daokoa/SoleSense2026/firmware/SoleSenseV2/state.h

// =============================================================================
// SoleSense v0.2 -- state.h
// Run state machine + request flags. The run is a simple state machine with
// a "paused" sub-state derived from AP client count.
// =============================================================================

#pragma once

#include <Arduino.h>

enum RunState : uint8_t { RS_IDLE = 0, RS_RECORDING = 1 };

// Top-level state. Set/cleared by the start/stop request handlers via the
// loop()-driven state machine in state.cpp.
extern volatile RunState gState;

// True only when gState==RS_RECORDING AND at least one client is on the AP.
// Sampling, FFT updates, and slot flushes only happen when this is true.
extern volatile bool gRunActive;

// Elapsed run time in ms, accumulated from intervals where gRunActive was true.
// THIS IS THE AUTHORITATIVE TIMER. Read by /api/run-state. Persisted to flash
// via storage.cpp.
extern volatile uint32_t gRunElapsedMs;

// Last millis() value when sampling was active. Used by state.cpp to advance
// gRunElapsedMs by the active delta on each loop tick.
extern volatile uint32_t gLastActiveMs;

// Total sample count for the current run (rolls back to 0 on /api/start).
extern volatile uint32_t gSampleCount;

// Time-domain step detection. Updated by step_detector_update() from
// process_sample() once per sample. Reset to 0 on /api/start.
//   gStepCount    -- total heel-strikes detected this run
//   gContactSumMs -- sum of valid heel-strike-to-toe-off durations
//   gContactCount -- number of valid contact intervals contributing to the sum
// Average contact time = gContactSumMs / gContactCount when count > 0.
extern volatile uint32_t gStepCount;
extern volatile uint32_t gContactSumMs;
extern volatile uint32_t gContactCount;

// Peak FSR rate-of-rise on the heel composite, in ADC counts per second.
// Updated per sample by SoleSenseV2.ino's process_sample(). The run-report
// handler converts it to body-weights-per-second (BW/s) using the FSR's
// known 10 kg saturation point and an assumed 70 kg body weight; that's
// the standard biomechanics loading-rate metric.
extern volatile float gMaxHeelJerk;

// IMU sensor fusion. gLastImuImpactMs is the run-elapsed time of the most
// recent vertical-acceleration impact (|az - mean(az)| > IMU_IMPACT_DELTA_MS2).
// gImuConnected is set true once Welford stddev on az exceeds a tiny floor --
// proxy for "the IMU is actually producing real samples". When false (IMU
// disconnected or zero motion), the step detector skips IMU validation.
extern volatile uint32_t gLastImuImpactMs;
extern volatile bool     gImuConnected;
extern volatile uint32_t gImuImpactCount;   // count of IMU impacts during the run

// Total foot pressure metric (sum of all 6 FSR channels) -- exposed via
// /api/run-report for diagnostics and for cross-checking against the
// any-zone-max strike signal.
extern volatile float gMaxTotalPressure;   // peak SUM(ch0..5) seen this run

// Time-domain step detector. Call once per sample from process_sample(),
// after the per-channel stats are fresh. Strike fires on a rising edge
// through STEP_RISE_THRESHOLD; toe-off fires on heel < peak x FALL_FRACTION
// or after MAX_CONTACT_MS (force-release). When the IMU is connected the
// strike must also be paired with a recent IMU impact to count -- kills
// the "lift the insole and squeeze it" false positive. heelMean/heelStddev
// are kept in the signature for the future EMA-baseline option.
void step_detector_update(float heelValue, float heelMean, float heelStddev,
                          uint32_t nowMs);

// Peak vertical jerk (|d(accel_z)/dt|) seen during the current run, in m/s^3.
// FSR 402 saturates at ~10 kg so it can't measure peak running force directly
// (running impact is 100-200 kg of ground reaction). Vertical jerk from the
// IMU does measure impact rate cleanly -- dividing by g (9.81 m/s^2) gives the
// loading rate in BW/s, the standard biomechanics unit. Reset to 0 on
// /api/start. Updated per sample by process_sample() in SoleSenseV2.ino.
extern volatile float gMaxJerkZ;

// Set true by the 500 Hz hardware-timer ISR. loop() drains this flag.
extern volatile bool gNewSample;

// HTTP-task -> loop() request flags. Handlers set these and return immediately;
// loop() observes them and performs the state transition.
extern volatile bool gStartRequested;
extern volatile bool gStopRequested;
extern volatile bool gSleepRequested;

// Pause-on-disconnect bookkeeping (state.cpp).
extern volatile uint32_t gPauseStartMs;     // millis() when last paused, 0 if not paused

// Set by state.cpp on resume (and on /api/start). process_sample() checks
// this on entry and clears its derivative-tracking statics (jerk-prev,
// anyZone-prev). Without this, the first sample after a pause computes
// jerk = (now - hours_old_value) and fires a false high_loading flag.
extern volatile bool gResetSampleTracking;

// Initialise state globals to known values (call from setup()).
void state_init();

// Drive the state machine: process request flags, observe AP station count,
// pause/resume gRunActive accordingly, advance gRunElapsedMs.
// Call once per loop() iteration before takeSample().
void state_tick();

// Convenience: human-readable label for the current state.
const char* state_name();
