daokoa/SoleSense2026/firmware/SoleSenseV2/sensors.h

// =============================================================================
// SoleSense -- sensors.h
// FSR matrix-scan + MPU-6050 reads. The matrix scheme uses 2 sets of 3 FSRs
// sharing 3 ADC pins, gated by two power lines (PIN_PWR_SET1/2).
// =============================================================================

#pragma once

#include <Arduino.h>
#include "config.h"

// Latest sensor reading globals (updated by sensors_read_all()).
//   gFsr[0..5] in raw ADC counts (0..4095) with zero-offset applied
//   gFsrEma[0..5] EMA-smoothed copy for the live UI display (less jittery
//     foot-circle fills than the raw signal). Step detector keeps using
//     raw gFsr -> Kalman; this is purely for visual smoothing.
//   gAccel[0..2] in m/s^2, offset applied
//   gGyro[0..2] in deg/s, offset applied
extern int16_t gFsr[N_FSR];
extern int16_t gFsrEma[N_FSR];
extern float   gAccel[3];
extern float   gGyro[3];

// EMA alpha for the FSR display filter. alpha=0.15 at 500 Hz gives a
// time-constant tau = -dt / ln(1-alpha) ~= 12 ms, which smooths the
// per-sample ADC noise without lagging the visual behind real presses.
static constexpr float FSR_EMA_ALPHA = 0.15f;

// Calibration offsets (loaded from NVS at boot, written by calibrate_*).
extern int   gFsrZero[N_FSR];
extern float gImuOffset[6];   // ax, ay, az, gx, gy, gz

// One-time hardware init: pin modes, ADC resolution, I2C, MPU-6050 wake.
void sensors_init();

// Read all 6 FSRs (set-scan) + IMU. Populates the globals above.
void sensors_read_all();

// Run an FSR zero calibration: 32 samples averaged with insole unloaded,
// store into gFsrZero[]. Caller is responsible for persisting to NVS.
void sensors_calibrate_fsr();

// Run an IMU zero calibration: 64 samples averaged with insole flat,
// store into gImuOffset[] (gravity stays on accel-Z).
void sensors_calibrate_imu();
