daokoa/SoleSense2026/firmware/SoleSenseV2/http_routes.cpp

// SoleSense v0.2 -- HTTP routes. Static UI + JSON API over the device AP.
// Route registration is in http_register_routes() at the bottom.

#include "http_routes.h"
#include "config.h"
#include "state.h"
#include "sensors.h"
#include "fft.h"
#include "outliers.h"
#include "stats.h"
#include "storage.h"
#include "auth.h"

#include <LittleFS.h>
#include <WiFi.h>
#include <math.h>

// -- Auth middleware ----------------------------------------------------------
// Returns true if the request carries a valid Bearer token. On false, sends
// a 401 response and the caller MUST return immediately.
static bool require_auth(AsyncWebServerRequest* req) {
  if (!req->hasHeader("Authorization")) {
    req->send(401, "application/json", "{\"ok\":false,\"error\":\"no auth\"}");
    return false;
  }
  String tok = auth_extract_bearer(req->header("Authorization"));
  if (tok.length() == 0 || !auth_check_token(tok)) {
    req->send(401, "application/json", "{\"ok\":false,\"error\":\"invalid token\"}");
    return false;
  }
  return true;
}

// Extract a JSON string field from a tiny request body. Caller-allocated buf.
// Returns true if found; this is a poor-man's parser sufficient for our needs
// (simple flat JSON like {"username":"x","pin":"1234"}).
static bool json_get_string(const String& body, const char* field,
                            char* out, size_t outlen) {
  String key = String("\"") + field + "\"";
  int k = body.indexOf(key);
  if (k < 0) return false;
  int colon = body.indexOf(':', k);
  if (colon < 0) return false;
  int q1 = body.indexOf('"', colon);
  if (q1 < 0) return false;
  int q2 = body.indexOf('"', q1 + 1);
  if (q2 < 0) return false;
  size_t n = q2 - q1 - 1;
  if (n >= outlen) n = outlen - 1;
  for (size_t i = 0; i < n; i++) out[i] = body[q1 + 1 + i];
  out[n] = 0;
  return true;
}

static bool json_get_number(const String& body, const char* field, float* out) {
  String key = String("\"") + field + "\"";
  int k = body.indexOf(key);
  if (k < 0) return false;
  int colon = body.indexOf(':', k);
  if (colon < 0) return false;
  size_t i = colon + 1;
  while (i < body.length() && (body[i] == ' ' || body[i] == '\t')) i++;
  // Capture until comma/brace
  String num;
  while (i < body.length() && body[i] != ',' && body[i] != '}') {
    num += body[i++];
  }
  num.trim();
  if (num.length() == 0) return false;
  *out = num.toFloat();
  return true;
}

// -- /api/device --------------------------------------------------------------
static void handle_device(AsyncWebServerRequest* req) {
  String j = "{";
  j += "\"firmware\":\"SoleSense ";  j += SS_FIRMWARE_VERSION; j += "\",";
  j += "\"version\":\"";              j += SS_FIRMWARE_VERSION; j += "\",";
  j += "\"board\":\"";                j += SS_BOARD_NAME;       j += "\",";
  j += "\"sampleRateHz\":";           j += SAMPLE_RATE_HZ;      j += ",";
  j += "\"heap_free\":";              j += (unsigned)ESP.getFreeHeap(); j += ",";
  j += "\"state\":\"";                j += state_name();        j += "\",";
  j += "\"fs\":{\"totalBytes\":";     j += (unsigned)LittleFS.totalBytes();
  j += ",\"usedBytes\":";             j += (unsigned)LittleFS.usedBytes(); j += "},";
  j += "\"thresholds_hardcoded\":true";
  j += "}";
  req->send(200, "application/json", j);
}

// -- /api/sensor --------------------------------------------------------------
static void handle_sensor(AsyncWebServerRequest* req) {
  // Only re-read when idle (during a recording, the sample loop keeps
  // gFsr/gAccel/gGyro fresh at SAMPLE_RATE_HZ).
  if (gState == RS_IDLE) sensors_read_all();
  char body[384];
  snprintf(body, sizeof(body),
    "{\"ax\":%.3f,\"ay\":%.3f,\"az\":%.3f,"
    "\"gx\":%.3f,\"gy\":%.3f,\"gz\":%.3f,"
    "\"fsr\":[%d,%d,%d,%d,%d,%d],"
    "\"fsrEma\":[%d,%d,%d,%d,%d,%d]}",
    gAccel[0], gAccel[1], gAccel[2],
    gGyro[0],  gGyro[1],  gGyro[2],
    gFsr[0],    gFsr[1],    gFsr[2],    gFsr[3],    gFsr[4],    gFsr[5],
    gFsrEma[0], gFsrEma[1], gFsrEma[2], gFsrEma[3], gFsrEma[4], gFsrEma[5]);
  req->send(200, "application/json", body);
}

// -- /api/start /api/stop /api/sleep ------------------------------------------
static void handle_start(AsyncWebServerRequest* req) {
  if (!require_auth(req)) return;
  if (gState != RS_IDLE) {
    req->send(409, "application/json", "{\"ok\":false,\"error\":\"already recording\"}");
    return;
  }
  gStartRequested = true;
  req->send(200, "application/json", "{\"ok\":true}");
}

static void handle_stop(AsyncWebServerRequest* req) {
  if (!require_auth(req)) return;
  if (gState != RS_RECORDING) {
    req->send(409, "application/json", "{\"ok\":false,\"error\":\"not recording\"}");
    return;
  }
  gStopRequested = true;
  req->send(200, "application/json", "{\"ok\":true}");
}

static void handle_sleep(AsyncWebServerRequest* req) {
  if (!require_auth(req)) return;
  if (gState == RS_RECORDING) {
    req->send(409, "application/json", "{\"ok\":false,\"error\":\"recording\"}");
    return;
  }
  gSleepRequested = true;
  req->send(200, "application/json", "{\"ok\":true}");
}

// -- /api/calibrate/zero /api/calibrate/imu -----------------------------------
static void handle_cal_zero(AsyncWebServerRequest* req) {
  if (!require_auth(req)) return;
  if (gState != RS_IDLE) {
    req->send(409, "application/json", "{\"ok\":false,\"error\":\"recording\"}");
    return;
  }
  sensors_calibrate_fsr();
  String j = "{\"ok\":true,\"fsrZero\":[";
  for (int i = 0; i < N_FSR; i++) { j += gFsrZero[i]; if (i < N_FSR-1) j += ","; }
  j += "]}";
  req->send(200, "application/json", j);
}

static void handle_cal_imu(AsyncWebServerRequest* req) {
  if (!require_auth(req)) return;
  if (gState != RS_IDLE) {
    req->send(409, "application/json", "{\"ok\":false,\"error\":\"recording\"}");
    return;
  }
  sensors_calibrate_imu();
  char body[200];
  snprintf(body, sizeof(body),
    "{\"ok\":true,\"accel\":[%.4f,%.4f,%.4f],\"gyro\":[%.4f,%.4f,%.4f]}",
    gImuOffset[0],gImuOffset[1],gImuOffset[2],
    gImuOffset[3],gImuOffset[4],gImuOffset[5]);
  req->send(200, "application/json", body);
}

// -- /api/run-state -----------------------------------------------------------
static void handle_run_state(AsyncWebServerRequest* req) {
  String j = "{";
  j += "\"recording\":";          j += (gState == RS_RECORDING ? "true" : "false"); j += ",";
  j += "\"run_active\":";         j += (gRunActive ? "true" : "false");             j += ",";
  j += "\"elapsed_ms\":";         j += (unsigned long)gRunElapsedMs;                j += ",";
  j += "\"sample_count\":";       j += (unsigned long)gSampleCount;                 j += ",";
  j += "\"clients_connected\":";  j += (unsigned)WiFi.softAPgetStationNum();        j += ",";
  j += "\"outlier_count\":";      j += (unsigned)outliers_count();
  j += "}";
  req->send(200, "application/json", j);
}

// -- /api/run-spectrum --------------------------------------------------------
static void handle_run_spectrum(AsyncWebServerRequest* req) {
  // Returns the FFT magnitudes per (channel, bin). Compact format:
  //   { "binsHz":[...], "channels":[{"name":"heel","mag":[...]}, ...] }
  String j = "{\"binsHz\":[";
  for (uint8_t b = 0; b < FFT_BINS_PER_CHAN; b++) {
    j += FFT_BIN_FREQS_HZ[b]; if (b < FFT_BINS_PER_CHAN-1) j += ",";
  }
  j += "],\"channels\":[";
  // Canonical 3-zone medial/lateral layout (Choi 2024), matching the
  // channel ordering in sensors.cpp::read_set_a/read_set_b and the foot
  // diagram in the SPA's heatmap renderer.
  static const char* CH_NAMES[N_CHANNELS_TOTAL] = {
    "heel_med","heel_lat","mid_med","mid_lat","fore_med","fore_lat",
    "ax","ay","az","gx","gy","gz"
  };
  for (uint8_t c = 0; c < N_CHANNELS_TOTAL; c++) {
    j += "{\"name\":\""; j += CH_NAMES[c]; j += "\",\"mag\":[";
    for (uint8_t b = 0; b < FFT_BINS_PER_CHAN; b++) {
      j += String(fft_get_magnitude(c, b), 4);
      if (b < FFT_BINS_PER_CHAN-1) j += ",";
    }
    j += "]}";
    if (c < N_CHANNELS_TOTAL-1) j += ",";
  }
  j += "]}";
  req->send(200, "application/json", j);
}

// -- /api/run-outliers --------------------------------------------------------
static void handle_run_outliers(AsyncWebServerRequest* req) {
  String j = "[";
  for (uint8_t i = 0; i < outliers_count(); i++) {
    const Outlier& o = outliers_at(i);
    j += "{\"ts\":";        j += (unsigned long)o.timestamp_ms;
    j += ",\"channel\":";   j += o.channel;
    j += ",\"value\":";     j += String(o.value, 3);
    j += ",\"sigma\":";     j += String(o.sigma, 2);
    j += "}";
    if (i < outliers_count()-1) j += ",";
  }
  j += "]";
  req->send(200, "application/json", j);
}

// -- /api/run-report ----------------------------------------------------------
// Computes the final metrics from the FFT bins + outlier buffer + running
// channel stats. All analysis runs on-device; the browser is a renderer.
//
// Channel index reminder (3-zone x medial/lateral layout, Choi 2024 +E-at-heel):
//   0 = heel medial,     1 = heel lateral
//   2 = midfoot medial,  3 = midfoot lateral
//   4 = forefoot medial, 5 = forefoot lateral   (sensors at the front, near
//                                                 the metatarsal heads /
//                                                 just behind the toe row)
//   6..8  = accel x/y/z
//   9..11 = gyro x/y/z
static void handle_run_report(AsyncWebServerRequest* req) {
  // -- Cadence + step count: time-domain heel-strike detector (state.cpp).
  // Each rising edge through max(floor, 4sigma) is a step; cadence is just
  // steps x 60 / runtime. Wait for >=2 s of recording before reporting cadence
  // so very-short-run noise doesn't produce a wild number.
  uint32_t durMs  = gRunElapsedMs;
  uint32_t durSec = durMs / 1000UL;
  int   steps   = (int)gStepCount;
  int   cadence = 0;
  // Show cadence as soon as we have a meaningful sample. Old gates (>=2 s,
  // >=60 spm) were too strict -- a 3-second test with 2 presses came out at
  // 40 spm and got clamped to 0, leaving the user staring at "--" on every
  // first run. Loosened to: >=1 s elapsed, >=1 step detected, result in a
  // very generous [20, 300] spm band (running peaks at ~200, finger
  // tapping caps near 300).
  if (durMs >= 1000UL && gStepCount > 0) {
    cadence = (int)((uint64_t)gStepCount * 60000ULL / (uint64_t)durMs);
    if (cadence < 20 || cadence > 300) cadence = 0;
  }

  // FSR saturation flag: per-channel peaks aren't tracked, so we use the
  // total-pressure ceiling as a proxy -- if the average peak across the six
  // FSRs is above ~3500 ADC counts, several channels likely hit the rail and
  // the loading-rate number underreports the real impact.
  bool fsrSaturated = (gMaxTotalPressure / (float)N_FSR) > 3500.0f;

  // -- Zone means (raw FSR units; the frontend percentage-ifies for display).
  // Three zones x two sensors each. Clamp negatives to 0 -- they only happen
  // when an FSR is unconnected and a stale calibration offset is in effect,
  // and a negative loading value isn't physically meaningful.
  auto clamp_pos = [](float v) { return v > 0.0f ? v : 0.0f; };
  float zHeel     = clamp_pos((stats_get_mean(0) + stats_get_mean(1)) * 0.5f);
  float zMidfoot  = clamp_pos((stats_get_mean(2) + stats_get_mean(3)) * 0.5f);
  float zForefoot = clamp_pos((stats_get_mean(4) + stats_get_mean(5)) * 0.5f);

  // -- Medial vs lateral on a single insole.
  // This is NOT left-foot vs right-foot -- the system has one insole. The split
  // is medial (inside-of-foot) vs lateral (outside-of-foot) loading. With the
  // 3x2 layout, medial = ch{0,2,4} and lateral = ch{1,3,5}.
  float medial  = (stats_get_mean(0) + stats_get_mean(2) + stats_get_mean(4)) / 3.0f;
  float lateral = (stats_get_mean(1) + stats_get_mean(3) + stats_get_mean(5)) / 3.0f;
  float mlTotal = medial + lateral;
  float medialPct  = mlTotal > 0.0f ? medial  / mlTotal * 100.0f : 50.0f;
  float lateralPct = mlTotal > 0.0f ? lateral / mlTotal * 100.0f : 50.0f;
  float asymPct    = fabsf(medialPct - lateralPct);

  // -- Heel-vs-forefoot strike ratio
  float hfTotal   = zHeel + zForefoot;
  float heelRatio = hfTotal > 0.0f ? zHeel / hfTotal * 100.0f : 50.0f;

  // -- Loading rate via FSR-jerk extrapolation.
  // FSR 402 saturates at ~10 kg of force, far below running peak GRF
  // (100-200 kg). But the *rate of rise* of the FSR signal during the
  // unsaturated portion of the impact transient encodes impact magnitude.
  //
  // Conversion uses:
  //   force_at_FSR_saturation = 10 kg x g = 98.1 N
  //   ADC at saturation        = 4095 (12-bit, full scale; assumed)
  //   user body weight         = gSession.body_kg if logged in, else 70 kg
  //   BW/s = (counts/s) x (98.1 / 4095) / (body_kg x 9.81)
  // Healthy runners read 30-80 BW/s; >80 raises stress-fracture risk
  // (Milner 2006).
  float bw_kg = gSession.active ? gSession.body_kg : 70.0f;
  float bw_n  = bw_kg * 9.81f;
  float loadingRateBWs = gMaxHeelJerk > 0.0f
                       ? gMaxHeelJerk * (98.1f / 4095.0f) / bw_n
                       : 0.0f;
  (void)gMaxJerkZ;   // IMU vertical jerk still tracked for future fusion

  // -- Pronation: running mean of gyro_x (degrees/s).
  // Net mean ~= 0 for symmetric gait; positive = pronation, negative = supination.
  // First-order only. Clamp to 0 if below the noise-floor (|x| < 0.5  deg/s,
  // well under the 8-15  deg/s flag thresholds) so the UI shows "0.0 deg" instead
  // of an ugly "-0.00 deg" when the IMU is disconnected or perfectly zeroed.
  float pronate = stats_get_mean(N_FSR + 3);   // channel 9 = gyro_x
  if (fabsf(pronate) < 0.5f) pronate = 0.0f;

  // -- Ground contact time: average of per-step heel-strike->toe-off intervals
  // recorded by the time-domain step detector. 0 until at least one valid
  // contact interval (frontend renders that as "--").
  float contactMs = gContactCount > 0
                  ? (float)gContactSumMs / (float)gContactCount
                  : 0.0f;
  (void)durSec;

  // -- Injury flags (research-based THRESH constants, see docs/research.md)
  String flags = "[";
  bool firstFlag = true;
  auto pushFlag = [&](const char* key, const String& val) {
    if (!firstFlag) flags += ",";
    flags += "{\"key\":\"";
    flags += key;
    flags += "\",\"val\":\"";
    flags += val;
    flags += "\"}";
    firstFlag = false;
  };

  if (heelRatio > 65.0f && zHeel > zForefoot + 10.0f) {
    pushFlag("heel_strike", String((int)heelRatio) + "% heel load");
  }
  // High-loading flag: > 80 BW/s. Threshold from biomechanics literature
  // (Milner 2006; Davis 2016): runners above this have ~2x the stress-fracture
  // risk vs. runners with loading rates < 60 BW/s.
  if (loadingRateBWs > 80.0f) {
    pushFlag("high_loading", String((int)loadingRateBWs) + " BW/s");
  }
  if (cadence > 0 && cadence < 160) {
    pushFlag("low_cadence", String(cadence) + " steps/min");
  }
  if (pronate > 15.0f) {
    pushFlag("overpronation", String(pronate, 1) + " deg/s");
  } else if (pronate < -8.0f) {
    pushFlag("supination", String(fabsf(pronate), 1) + " deg/s outward");
  }
  if (asymPct > 10.0f) {
    pushFlag("medial_lateral_asym",
             String((int)medialPct) + "% med / " + String((int)lateralPct) + "% lat");
  }
  // FSR saturation flag -- alerts the user that the loading-rate number
  // is a lower bound (the FSR peaked out before it could measure the real impact).
  if (fsrSaturated) {
    pushFlag("fsr_saturated", "loading rate may be underreported");
  }
  flags += "]";

  // -- Build response.
  // v0.2 schema: medialPct/lateralPct (not lPct/rPct), loadingSigma (not
  // loadingRate BW/s), contactMs reports 0 when unmeasured. Frontend uses
  // these new keys and shows "--" for any value at 0.
  String j = "{";
  j += "\"steps\":";        j += steps;                     j += ",";
  j += "\"cadence\":";      j += cadence;                   j += ",";
  j += "\"durSec\":";       j += (unsigned long)durSec;     j += ",";
  j += "\"contactMs\":";    j += String(contactMs, 1);      j += ",";
  j += "\"loadingRate\":";  j += String(loadingRateBWs, 1); j += ",";
  j += "\"pronate\":";      j += String(pronate, 2);        j += ",";
  j += "\"medialPct\":";    j += String(medialPct, 1);      j += ",";
  j += "\"lateralPct\":";   j += String(lateralPct, 1);     j += ",";
  j += "\"zoneAvg\":{";
  j +=   "\"heel\":";       j += String(zHeel, 1);          j += ",";
  j +=   "\"midfoot\":";    j += String(zMidfoot, 1);       j += ",";
  j +=   "\"forefoot\":";   j += String(zForefoot, 1);
  j += "},";
  j += "\"flags\":";        j += flags;                     j += ",";
  j += "\"durationMs\":";   j += (unsigned long)durMs;      j += ",";
  j += "\"samples\":";      j += (unsigned long)gSampleCount; j += ",";
  j += "\"outliers\":";     j += (unsigned)outliers_count(); j += ",";
  // Per-user body profile (used by the frontend to derive stride length,
  // estimated speed, and any height-normalized display). Falls back to
  // safe defaults when no session is active so /api/run-report stays
  // useful for debug calls without authentication.
  float prof_kg = gSession.active ? gSession.body_kg   : 70.0f;
  float prof_cm = gSession.active ? gSession.height_cm : 170.0f;
  j += "\"profile\":{";
  j +=   "\"body_kg\":";   j += String(prof_kg, 1);
  j +=   ",\"height_cm\":"; j += String(prof_cm, 1);
  j += "},";
  // Diagnostic / sensor-fusion fields (frontend may ignore).
  j += "\"imuConnected\":"; j += (gImuConnected ? "true":"false"); j += ",";
  j += "\"imuImpacts\":";   j += (unsigned long)gImuImpactCount; j += ",";
  j += "\"maxTotalPressure\":"; j += String(gMaxTotalPressure, 0);
  j += "}";
  req->send(200, "application/json", j);
}

// -- Debug: /api/fft-selftest -------------------------------------------------
// Runs the canned 2-Hz-sine validation; expects ~100 mag in the 2 Hz bin.
// Output goes to Serial Monitor; HTTP response is just an ack. Refuses while
// recording to avoid trampling live state.
static void handle_fft_selftest(AsyncWebServerRequest* req) {
  if (gState != RS_IDLE) {
    req->send(409, "application/json", "{\"ok\":false,\"error\":\"recording\"}");
    return;
  }
  fft_self_test();
  req->send(200, "application/json", "{\"ok\":true,\"see\":\"Serial Monitor\"}");
}

// -- Debug: /api/storage-selftest ---------------------------------------------
// Writes 3 slots, corrupts the newest, asserts load_latest falls back. Cleans
// up after itself. Refuses during a recording (would clobber real slots).
static void handle_storage_selftest(AsyncWebServerRequest* req) {
  if (gState != RS_IDLE) {
    req->send(409, "application/json", "{\"ok\":false,\"error\":\"recording\"}");
    return;
  }
  storage_self_test();
  req->send(200, "application/json", "{\"ok\":true,\"see\":\"Serial Monitor\"}");
}

// -- /api/storage-state -------------------------------------------------------
// Diagnostic: how many slots are currently valid, and what's the newest header.
static void handle_storage_state(AsyncWebServerRequest* req) {
  uint8_t count = storage_valid_slot_count();
  SlotHeader hdr;
  bool has = storage_load_latest(hdr);
  String j = "{\"valid_slots\":";
  j += count;
  if (has) {
    j += ",\"latest\":{";
    j += "\"slot_n\":";        j += (unsigned long)hdr.slot_n;
    j += ",\"timestamp_ms\":"; j += (unsigned long)hdr.timestamp_ms;
    j += ",\"sample_count\":"; j += (unsigned long)hdr.sample_count;
    j += ",\"run_done\":";     j += (unsigned long)hdr.run_done;
    j += "}";
  } else {
    j += ",\"latest\":null";
  }
  j += "}";
  req->send(200, "application/json", j);
}

// -- /api/auth/* --------------------------------------------------------------
// Public state endpoint: tells the frontend whether to show login or
// claim-mode (first-user registration), and current account usage so the
// signup form can warn if the device is full.
static void handle_auth_state(AsyncWebServerRequest* req) {
  String j = "{";
  j += "\"ownerExists\":";    j += (auth_owner_exists() ? "true" : "false");
  j += ",\"sessionActive\":"; j += (gSession.active     ? "true" : "false");
  j += ",\"username\":\"";    j += (gSession.active ? gSession.username : "");
  j += "\",\"userCount\":";   j += auth_user_count();
  j += ",\"maxUsers\":";      j += MAX_USERS;
  j += "}";
  req->send(200, "application/json", j);
}

// Register a new user. URL-encoded body: username, pin, body_kg, height_cm.
// Self-signup: anyone connected to the AP can create an account. The shared
// WiFi password already gates network access; layering an owner-token check
// on top would block a legitimate household member from making themselves
// an account. The new user is auto-logged-in atomically.
static void handle_auth_register(AsyncWebServerRequest* req) {
  String username  = req->arg("username");
  String pin       = req->arg("pin");
  float  body_kg   = req->arg("body_kg").toFloat();
  float  height_cm = req->arg("height_cm").toFloat();
  int rc = auth_register(username, pin, body_kg, height_cm);
  if (rc == 0) {
    String j = "{\"ok\":true,\"token\":\"";
    j += gSession.token_hex;
    j += "\",\"body_kg\":";   j += String(gSession.body_kg, 1);
    j += ",\"height_cm\":";   j += String(gSession.height_cm, 1);
    j += ",\"username\":\""; j += gSession.username; j += "\"}";
    req->send(200, "application/json", j);
    return;
  }
  // Granular error -> specific human-readable message.
  const char* err =
    (rc == -1) ? "Username already taken -- pick another." :
    (rc == -2) ? "Could not save (NVS error). Try again." :
    (rc == -3) ? "Username must be 4-13 letters, digits, or underscore." :
    (rc == -4) ? "PIN must be 4-16 digits." :
    (rc == -5) ? "Body weight must be 25-250 kg." :
    (rc == -8) ? "Height must be 100-250 cm." :
    (rc == -6) ? "This device is full (account limit reached). "
                 "Ask the owner to factory-reset to free up space." :
    (rc == -7) ? "Too many signups too fast. Wait a minute and try again." :
                 "Invalid input.";
  // 429 for rate-limit, 507 for capacity, 400 for everything else.
  int status = (rc == -6) ? 507 : (rc == -7) ? 429 : 400;
  String j = "{\"ok\":false,\"error\":\""; j += err; j += "\"}";
  req->send(status, "application/json", j);
}

// Login. URL-encoded body: username, pin.
static void handle_auth_login(AsyncWebServerRequest* req) {
  String username = req->arg("username");
  String pin      = req->arg("pin");
  int rc = auth_login(username, pin);
  if (rc == 0) {
    String j = "{\"ok\":true,\"token\":\"";
    j += gSession.token_hex;
    j += "\",\"body_kg\":";  j += String(gSession.body_kg, 1);
    j += ",\"height_cm\":";  j += String(gSession.height_cm, 1);
    j += ",\"username\":\""; j += gSession.username; j += "\"";
    j += "}";
    req->send(200, "application/json", j);
    return;
  }
  if (rc == -3) {
    req->send(429, "application/json",
              "{\"ok\":false,\"error\":\"Too many attempts -- locked for 30 seconds.\"}");
    return;
  }
  // -1 unknown user, -2 wrong PIN: collapse to one message so attackers
  // can't enumerate which usernames exist.
  req->send(401, "application/json",
            "{\"ok\":false,\"error\":\"Username or PIN is incorrect.\"}");
}

static void handle_auth_logout(AsyncWebServerRequest* req) {
  if (!require_auth(req)) return;
  auth_logout();
  req->send(200, "application/json", "{\"ok\":true}");
}

static void handle_auth_profile(AsyncWebServerRequest* req) {
  if (!require_auth(req)) return;
  String j = "{\"username\":\""; j += gSession.username;
  j += "\",\"body_kg\":";   j += String(gSession.body_kg, 1);
  j += ",\"height_cm\":";   j += String(gSession.height_cm, 1);
  j += "}";
  req->send(200, "application/json", j);
}

// POST /api/auth/profile -- edit body_kg and/or height_cm for the signed-in
// user. URL-encoded body, both fields optional. Returns the updated profile.
static void handle_auth_profile_update(AsyncWebServerRequest* req) {
  if (!require_auth(req)) return;
  float body_kg = NAN, height_cm = NAN;
  if (req->hasArg("body_kg"))   body_kg   = req->arg("body_kg").toFloat();
  if (req->hasArg("height_cm")) height_cm = req->arg("height_cm").toFloat();
  int rc = auth_update_profile(body_kg, height_cm);
  if (rc == 0) {
    String j = "{\"ok\":true,\"username\":\""; j += gSession.username;
    j += "\",\"body_kg\":";   j += String(gSession.body_kg, 1);
    j += ",\"height_cm\":";   j += String(gSession.height_cm, 1);
    j += "}";
    req->send(200, "application/json", j);
    return;
  }
  const char* err =
    (rc == -1) ? "Sign in first." :
    (rc == -2) ? "Nothing to update." :
    (rc == -3) ? "Body weight must be 25-250 kg." :
    (rc == -4) ? "Height must be 100-250 cm." :
    (rc == -5 || rc == -6) ? "Could not save (NVS error). Try again." :
                 "Invalid input.";
  String j = "{\"ok\":false,\"error\":\""; j += err; j += "\"}";
  req->send(400, "application/json", j);
}

// POST /api/data/clear -- wipe the run-snapshot ring buffer on flash.
// In-memory peak counters (gMaxTotalPressure, gMaxHeelJerk, ...) reset
// automatically on the next Start Run.
static void handle_data_clear(AsyncWebServerRequest* req) {
  if (!require_auth(req)) return;
  if (gState != RS_IDLE) {
    req->send(409, "application/json",
              "{\"ok\":false,\"error\":\"Stop the current run first.\"}");
    return;
  }
  storage_clear();
  req->send(200, "application/json", "{\"ok\":true}");
}

// -- Registration -------------------------------------------------------------
void http_register_routes(AsyncWebServer& server) {
  server.on("/api/device",         HTTP_GET,  handle_device);
  server.on("/api/sensor",         HTTP_GET,  handle_sensor);
  server.on("/api/start",          HTTP_POST, handle_start);
  server.on("/api/stop",           HTTP_POST, handle_stop);
  server.on("/api/sleep",          HTTP_POST, handle_sleep);
  server.on("/api/calibrate/zero", HTTP_POST, handle_cal_zero);
  server.on("/api/calibrate/imu",  HTTP_POST, handle_cal_imu);
  server.on("/api/run-state",      HTTP_GET,  handle_run_state);
  server.on("/api/run-spectrum",   HTTP_GET,  handle_run_spectrum);
  server.on("/api/run-outliers",   HTTP_GET,  handle_run_outliers);
  server.on("/api/run-report",     HTTP_GET,  handle_run_report);
  server.on("/api/fft-selftest",     HTTP_POST, handle_fft_selftest);
  server.on("/api/storage-selftest", HTTP_POST, handle_storage_selftest);
  server.on("/api/storage-state",    HTTP_GET,  handle_storage_state);
  // Auth (owner-claim, login, logout, profile)
  server.on("/api/auth/state",     HTTP_GET,  handle_auth_state);
  server.on("/api/auth/register",  HTTP_POST, handle_auth_register);
  server.on("/api/auth/login",     HTTP_POST, handle_auth_login);
  server.on("/api/auth/logout",    HTTP_POST, handle_auth_logout);
  server.on("/api/auth/profile",   HTTP_GET,  handle_auth_profile);
  server.on("/api/auth/profile",   HTTP_POST, handle_auth_profile_update);
  server.on("/api/data/clear",     HTTP_POST, handle_data_clear);

  server.serveStatic("/", LittleFS, "/").setDefaultFile("index.html");
}
