daokoa/SoleSense2026/firmware/SoleSenseV2/auth.cpp

// =============================================================================
// SoleSense v0.2 -- auth.cpp
// =============================================================================
#include "auth.h"

#include <Preferences.h>
#include <mbedtls/sha256.h>
#include <esp_random.h>

Session gSession;

static Preferences sNvs;
static constexpr const char* NS = "solesense_auth";

// In-RAM sliding-window rate limiter for /api/auth/register. Stores
// timestamps (millis) of the last REG_RATE_MAX_PER_WINDOW successful
// registrations. If the oldest of those is within REG_RATE_WINDOW_MS, the
// next request is rejected. Per-AP, not per-IP -- sharing one AP means one
// limiter is enough.
static uint32_t sRegTimestamps[REG_RATE_MAX_PER_WINDOW] = {0};

static bool reg_rate_check_and_record() {
  const uint32_t now = millis();
  // Find the slot with the oldest timestamp.
  uint8_t oldest = 0;
  for (uint8_t i = 1; i < REG_RATE_MAX_PER_WINDOW; i++) {
    if (sRegTimestamps[i] < sRegTimestamps[oldest]) oldest = i;
  }
  // If the oldest slot is still inside the window AND populated, deny.
  if (sRegTimestamps[oldest] != 0 &&
      (now - sRegTimestamps[oldest]) < REG_RATE_WINDOW_MS) {
    return false;
  }
  sRegTimestamps[oldest] = now;
  return true;
}

// -- In-memory rate limiter --------------------------------------------------
// Per-username, slot-allocated. Plenty for a single-insole device.
struct FailEntry {
  char     user[32];
  uint8_t  count;
  uint32_t window_start_ms;
  uint32_t lockout_until_ms;
};
static constexpr uint8_t MAX_FAIL_SLOTS = 8;
static FailEntry sFails[MAX_FAIL_SLOTS] = {};

static FailEntry* find_or_alloc_fail(const String& user) {
  // Look for existing slot.
  for (auto& e : sFails) {
    if (strncmp(e.user, user.c_str(), sizeof(e.user)) == 0) return &e;
  }
  // Take the oldest unused / least recently failed slot.
  FailEntry* oldest = &sFails[0];
  for (auto& e : sFails) {
    if (e.user[0] == 0) { oldest = &e; break; }
    if (e.window_start_ms < oldest->window_start_ms) oldest = &e;
  }
  memset(oldest, 0, sizeof(*oldest));
  strncpy(oldest->user, user.c_str(), sizeof(oldest->user) - 1);
  return oldest;
}

// -- SHA-256 helper -----------------------------------------------------------
static void sha256_concat(const uint8_t* a, size_t alen,
                          const uint8_t* b, size_t blen,
                          uint8_t out[32]) {
  mbedtls_sha256_context ctx;
  mbedtls_sha256_init(&ctx);
  mbedtls_sha256_starts(&ctx, 0);
  mbedtls_sha256_update(&ctx, a, alen);
  mbedtls_sha256_update(&ctx, b, blen);
  mbedtls_sha256_finish(&ctx, out);
  mbedtls_sha256_free(&ctx);
}

static void random_bytes(uint8_t* buf, size_t n) {
  for (size_t i = 0; i < n; i += 4) {
    uint32_t r = esp_random();
    size_t take = (n - i) < 4 ? (n - i) : 4;
    memcpy(buf + i, &r, take);
  }
}

static void hex_encode(const uint8_t* in, size_t n, char* out) {
  static const char* H = "0123456789abcdef";
  for (size_t i = 0; i < n; i++) {
    out[i*2]     = H[(in[i] >> 4) & 0xF];
    out[i*2 + 1] = H[in[i] & 0xF];
  }
  out[n*2] = 0;
}

// NVS key names are limited to 15 characters. Use a 2-char prefix per field
// + the username, giving us 13 chars for the username. Validation in
// auth_register enforces this. Prefixes are lowercase letters; the global
// "owner_user" key is distinct and won't collide.
static String key_for(const char* user, char prefix) {
  String s;
  s.reserve(15);
  s += prefix;
  s += '_';
  s += user;
  return s;
}

// Validation helpers. Username 4-13 chars [a-zA-Z0-9_]; PIN 4-16 digits.
static bool valid_username(const String& u) {
  if (u.length() < 4 || u.length() > 13) return false;
  for (size_t i = 0; i < u.length(); i++) {
    char c = u[i];
    bool ok = (c >= 'a' && c <= 'z') ||
              (c >= 'A' && c <= 'Z') ||
              (c >= '0' && c <= '9') ||
              c == '_';
    if (!ok) return false;
  }
  return true;
}

static bool valid_pin(const String& p) {
  if (p.length() < 4 || p.length() > 16) return false;
  for (size_t i = 0; i < p.length(); i++) {
    if (p[i] < '0' || p[i] > '9') return false;
  }
  return true;
}

// -- Public API ---------------------------------------------------------------
void auth_init() {
  sNvs.begin(NS, false);
  // Nothing else to bootstrap -- owner detection happens lazily.
  Serial.printf("[Auth] init; ownerExists=%s\n",
                auth_owner_exists() ? "yes" : "no");
}

bool auth_owner_exists() {
  return sNvs.isKey("owner_user");
}

bool auth_in_claim_mode() {
  return !auth_owner_exists();
}

uint16_t auth_user_count() {
  return sNvs.getUShort("uc", 0);
}

int auth_register(const String& username, const String& pin, float body_kg, float height_cm) {
  // Granular validation so handle_auth_register can return a specific
  // human-readable error, instead of a generic "invalid input".
  if (!valid_username(username)) return -3;   // bad username
  if (!valid_pin(pin))           return -4;   // bad PIN
  if (body_kg < 25.0f || body_kg > 250.0f) return -5;   // bad body weight
  if (height_cm < 100.0f || height_cm > 250.0f) return -8; // bad height

  // Anti-abuse caps. Both must pass BEFORE any state mutation.
  if (auth_user_count() >= MAX_USERS) {
    Serial.printf("[Auth] register denied: at user cap (%u)\n",
                  (unsigned)MAX_USERS);
    return -6;
  }
  if (!reg_rate_check_and_record()) {
    Serial.println("[Auth] register denied: rate limit");
    return -7;
  }

  // Capture claim-mode state BEFORE we mutate it.
  const bool wasClaimMode = auth_in_claim_mode();

  // Username taken? Check with isKey on the salt key (matches the type we wrote).
  const String saltKey   = key_for(username.c_str(), 's');
  const String hashKey   = key_for(username.c_str(), 'h');
  const String bodyKey   = key_for(username.c_str(), 'w');
  const String heightKey = key_for(username.c_str(), 't');
  if (sNvs.isKey(saltKey.c_str())) return -1;

  uint8_t salt[16];
  random_bytes(salt, sizeof(salt));
  uint8_t hash[32];
  sha256_concat((const uint8_t*)pin.c_str(), pin.length(), salt, sizeof(salt), hash);

  // -- Atomic write with rollback on partial failure ----------------------
  // NVS is per-key transactional but our profile = three keys. If any one
  // fails (out of space, hardware glitch), the partial state would lock
  // the username slot -- isKey(saltKey) would return true but the hash
  // would be missing, so login can never succeed. We roll back to a clean
  // state on any failure so the user can retry with the same username.
  size_t w1 = sNvs.putBytes(saltKey.c_str(), salt, sizeof(salt));
  if (w1 != sizeof(salt)) {
    Serial.printf("[Auth] register NVS w1=%u FAIL -- aborting cleanly\n",
                  (unsigned)w1);
    sNvs.remove(saltKey.c_str());   // no-op if not present
    return -2;
  }
  size_t w2 = sNvs.putBytes(hashKey.c_str(), hash, sizeof(hash));
  if (w2 != sizeof(hash)) {
    Serial.printf("[Auth] register NVS w2=%u FAIL -- rolling back\n",
                  (unsigned)w2);
    sNvs.remove(saltKey.c_str());
    sNvs.remove(hashKey.c_str());
    return -2;
  }
  size_t w3 = sNvs.putFloat(bodyKey.c_str(), body_kg);
  if (w3 == 0) {
    Serial.printf("[Auth] register NVS w3=0 FAIL -- rolling back\n");
    sNvs.remove(saltKey.c_str());
    sNvs.remove(hashKey.c_str());
    sNvs.remove(bodyKey.c_str());
    return -2;
  }
  size_t w4 = sNvs.putFloat(heightKey.c_str(), height_cm);
  if (w4 == 0) {
    Serial.printf("[Auth] register NVS w4=0 FAIL -- rolling back\n");
    sNvs.remove(saltKey.c_str());
    sNvs.remove(hashKey.c_str());
    sNvs.remove(bodyKey.c_str());
    sNvs.remove(heightKey.c_str());
    return -2;
  }

  // Bump user-count after all writes succeed. If this write fails, log it
  // but proceed -- the counter drift is recoverable on factory_reset and
  // doesn't affect login/list functionality.
  const uint16_t newCount = auth_user_count() + 1;
  if (sNvs.putUShort("uc", newCount) == 0) {
    Serial.println("[Auth] user count write failed (non-fatal)");
  }
  if (wasClaimMode) {
    sNvs.putString("owner_user", username);
  }
  Serial.printf("[Auth] register OK user='%s' count=%u/%u%s\n",
                username.c_str(), (unsigned)newCount, (unsigned)MAX_USERS,
                wasClaimMode ? " (claim)" : "");

  // Self-signup: always auto-login the freshly-created user.
  return auth_login(username, pin);
}

int auth_login(const String& username, const String& pin) {
  // Rate limit
  {
    FailEntry* fe = find_or_alloc_fail(username);
    if (fe->lockout_until_ms != 0 && (int32_t)(millis() - fe->lockout_until_ms) < 0) {
      return -3;
    }
  }

  if (!valid_username(username)) return -1;

  String saltKey = key_for(username.c_str(), 's');
  if (!sNvs.isKey(saltKey.c_str())) {
    auth_record_failure_and_check_lockout(username);
    return -1;
  }
  uint8_t salt[16];
  size_t saltLen = sNvs.getBytes(saltKey.c_str(), salt, sizeof(salt));
  if (saltLen != sizeof(salt)) return -1;

  uint8_t storedHash[32];
  size_t hashLen = sNvs.getBytes(key_for(username.c_str(), 'h').c_str(),
                                 storedHash, sizeof(storedHash));
  if (hashLen != sizeof(storedHash)) return -1;

  uint8_t computed[32];
  sha256_concat((const uint8_t*)pin.c_str(), pin.length(), salt, sizeof(salt), computed);

  if (memcmp(storedHash, computed, sizeof(computed)) != 0) {
    auth_record_failure_and_check_lockout(username);
    return -2;
  }

  // Build session
  uint8_t tok[32];
  random_bytes(tok, sizeof(tok));
  gSession.active = true;
  strncpy(gSession.username, username.c_str(), sizeof(gSession.username) - 1);
  gSession.username[sizeof(gSession.username) - 1] = 0;
  hex_encode(tok, sizeof(tok), gSession.token_hex);
  gSession.expires_ms = millis() + SESSION_IDLE_MS;
  gSession.body_kg    = sNvs.getFloat(key_for(username.c_str(), 'w').c_str(), 70.0f);
  gSession.height_cm  = sNvs.getFloat(key_for(username.c_str(), 't').c_str(), 170.0f);

  // Reset failure count for this user
  for (auto& e : sFails) {
    if (strncmp(e.user, username.c_str(), sizeof(e.user)) == 0) {
      memset(&e, 0, sizeof(e));
    }
  }

  Serial.printf("[Auth] login ok user=%s body_kg=%.1f height_cm=%.1f\n",
                gSession.username, gSession.body_kg, gSession.height_cm);
  return 0;
}

void auth_logout() {
  if (gSession.active) {
    Serial.printf("[Auth] logout user=%s\n", gSession.username);
  }
  memset(&gSession, 0, sizeof(gSession));
}

bool auth_check_token(const String& token) {
  if (!gSession.active) return false;
  if (token.length() != 64) return false;
  if (strncmp(token.c_str(), gSession.token_hex, 64) != 0) return false;
  if ((int32_t)(millis() - gSession.expires_ms) >= 0) {
    Serial.printf("[Auth] session expired user=%s\n", gSession.username);
    auth_logout();
    return false;
  }
  // Push deadline forward
  gSession.expires_ms = millis() + SESSION_IDLE_MS;
  return true;
}

String auth_extract_bearer(const String& header) {
  if (!header.startsWith("Bearer ")) return "";
  return header.substring(7);
}

int auth_update_profile(float body_kg, float height_cm) {
  if (!gSession.active) return -1;
  const bool wantBody   = !isnan(body_kg);
  const bool wantHeight = !isnan(height_cm);
  if (!wantBody && !wantHeight) return -2;          // nothing to change
  if (wantBody   && (body_kg   < 25.0f  || body_kg   > 250.0f)) return -3;
  if (wantHeight && (height_cm < 100.0f || height_cm > 250.0f)) return -4;

  // NVS-first, gSession-second so a failed write doesn't desync.
  if (wantBody) {
    const String bodyKey = key_for(gSession.username, 'w');
    if (sNvs.putFloat(bodyKey.c_str(), body_kg) == 0) return -5;
    gSession.body_kg = body_kg;
  }
  if (wantHeight) {
    const String heightKey = key_for(gSession.username, 't');
    if (sNvs.putFloat(heightKey.c_str(), height_cm) == 0) return -6;
    gSession.height_cm = height_cm;
  }
  Serial.printf("[Auth] profile updated user=%s body_kg=%.1f height_cm=%.1f\n",
                gSession.username, gSession.body_kg, gSession.height_cm);
  return 0;
}

void auth_factory_reset() {
  Serial.println("[Auth] FACTORY RESET -- wiping all profiles");
  sNvs.clear();
  memset(&gSession, 0, sizeof(gSession));
  memset(sFails, 0, sizeof(sFails));
  Serial.println("[Auth] reset complete; device is back in claim mode");
}

void auth_serial_console_tick() {
  // Accumulate a line buffer; act on each newline.
  static char  line[64];
  static uint8_t pos = 0;
  while (Serial.available()) {
    int c = Serial.read();
    if (c < 0) break;
    if (c == '\r') continue;
    if (c == '\n') {
      line[pos] = 0;
      if (strcmp(line, "factory_reset") == 0) {
        auth_factory_reset();
      } else if (pos > 0) {
        Serial.printf("[Console] unknown command: %s\n", line);
        Serial.println("  available: factory_reset");
      }
      pos = 0;
    } else if (pos < sizeof(line) - 1) {
      line[pos++] = (char)c;
    }
  }
}

bool auth_record_failure_and_check_lockout(const String& username) {
  FailEntry* fe = find_or_alloc_fail(username);
  uint32_t now = millis();
  // Expire window after 60 s
  if (now - fe->window_start_ms > 60000UL) {
    fe->window_start_ms = now;
    fe->count = 0;
  }
  fe->count++;
  if (fe->count >= 3) {
    fe->lockout_until_ms = now + 30000UL;   // 30 s lockout
    Serial.printf("[Auth] lockout user=%s for 30 s\n", username.c_str());
    return true;
  }
  return false;
}
