daokoa/SoleSense2026/firmware/SoleSenseV2/fft.cpp

// =============================================================================
// SoleSense v0.2 -- fft.cpp
//
// Windowed Goertzel implementation. Validated by feeding a known 2.0 Hz sine
// wave through fft_self_test() -- see end of file.
//
// Math reference: Wikipedia "Goertzel algorithm" "Computing the magnitude
// from intermediate values" -- we use the complex form because it gives the
// correct amplitude scaling, not just power.
// =============================================================================

#include "fft.h"

#include <math.h>

// Bin frequencies. At Fs=500 Hz and N=1024 the bin width is Fs/N ~= 0.488 Hz,
// so these are quantised to the nearest representable frequency at runtime.
//
// Layout reflects what running biomechanics actually has signal at:
//   * 0.5-3 Hz: cadence band (90-180 spm = 1.5-3 Hz per foot)
//   * 3.5-10 Hz: stride-cycle harmonics (swing-phase oscillations, leg
//                  recovery dynamics)
//   * 15-80 Hz: ground-impact transient content; FSR rising-edge harmonics
//                that the FSR-jerk extrapolation will key off of
//   * 150 Hz: vibration / shoe-slap content, high-frequency anomaly probe
const float FFT_BIN_FREQS_HZ[FFT_BINS_PER_CHAN] = {
  0.5f, 1.0f, 1.5f, 2.0f, 2.5f, 3.0f,        // cadence (6)
  3.5f, 4.0f, 5.0f, 7.5f, 10.0f,             // stride harmonics (5)
  15.0f, 20.0f, 30.0f, 50.0f, 80.0f, 120.0f, // impact band (6)
  150.0f                                      // vibration probe (1)
};

// Per-bin precomputed factors. Goertzel coef = 2*cos(omega) drives the
// recurrence; cos/sin separately drive the final magnitude.
static float sCoef[FFT_BINS_PER_CHAN];
static float sCos [FFT_BINS_PER_CHAN];
static float sSin [FFT_BINS_PER_CHAN];

// Per (channel, bin) recurrence state for the in-progress window.
//   q1 = s_{n-1},  q2 = s_{n-2}
static float sQ1[N_CHANNELS_TOTAL][FFT_BINS_PER_CHAN];
static float sQ2[N_CHANNELS_TOTAL][FFT_BINS_PER_CHAN];

// Per-channel sample counter for the in-progress window (0..FFT_WIN_SIZE-1).
static uint16_t sWinCount[N_CHANNELS_TOTAL];

// Number of completed windows per channel (monotonic).
static uint16_t sWinDone[N_CHANNELS_TOTAL];

// Most recent finalized magnitude per (channel, bin). What
// fft_get_magnitude() returns.
static float sMag[N_CHANNELS_TOTAL][FFT_BINS_PER_CHAN];

// -----------------------------------------------------------------------------
void fft_init() {
  for (uint8_t b = 0; b < FFT_BINS_PER_CHAN; b++) {
    // Quantise to the closest representable bin frequency for this window.
    // (Goertzel still works for arbitrary frequencies, but accuracy is best
    // when the frequency is at an exact bin centre.)
    float k     = roundf(FFT_BIN_FREQS_HZ[b] * (float)FFT_WIN_SIZE / (float)SAMPLE_RATE_HZ);
    float omega = 2.0f * (float)M_PI * k / (float)FFT_WIN_SIZE;
    sCos [b] = cosf(omega);
    sSin [b] = sinf(omega);
    sCoef[b] = 2.0f * sCos[b];
  }
  fft_reset();
}

void fft_reset() {
  for (uint8_t c = 0; c < N_CHANNELS_TOTAL; c++) {
    sWinCount[c] = 0;
    sWinDone [c] = 0;
    for (uint8_t b = 0; b < FFT_BINS_PER_CHAN; b++) {
      sQ1 [c][b] = 0.0f;
      sQ2 [c][b] = 0.0f;
      sMag[c][b] = 0.0f;
    }
  }
}

// Finalise the window for one channel: read complex DFT, convert to amplitude,
// stash into sMag, zero the recurrence state.
static void finalise_window(uint8_t c) {
  for (uint8_t b = 0; b < FFT_BINS_PER_CHAN; b++) {
    float q1 = sQ1[c][b];
    float q2 = sQ2[c][b];
    float real = q1 - q2 * sCos[b];
    float imag =      q2 * sSin[b];
    // 2/N converts the Goertzel "energy" output to single-sided amplitude
    // (so a pure sine of amplitude A at this bin reads as A).
    sMag[c][b] = sqrtf(real*real + imag*imag) * 2.0f / (float)FFT_WIN_SIZE;
    sQ1[c][b]  = 0.0f;
    sQ2[c][b]  = 0.0f;
  }
  sWinCount[c] = 0;
  sWinDone [c]++;
}

void fft_process_sample(uint8_t c, float sample, float running_mean) {
  if (c >= N_CHANNELS_TOTAL) return;

  // DC removal: subtract running mean so non-zero-mean signals (FSR ADC
  // readings, gravity-loaded accel-Z) don't smear into low-frequency bins.
  float x = sample - running_mean;

  for (uint8_t b = 0; b < FFT_BINS_PER_CHAN; b++) {
    float q0 = x + sCoef[b] * sQ1[c][b] - sQ2[c][b];
    sQ2[c][b] = sQ1[c][b];
    sQ1[c][b] = q0;
  }

  sWinCount[c]++;
  if (sWinCount[c] >= FFT_WIN_SIZE) finalise_window(c);
}

float fft_get_magnitude(uint8_t c, uint8_t b) {
  if (c >= N_CHANNELS_TOTAL || b >= FFT_BINS_PER_CHAN) return 0.0f;
  return sMag[c][b];
}

uint16_t fft_window_count(uint8_t c) {
  if (c >= N_CHANNELS_TOTAL) return 0;
  return sWinDone[c];
}

uint8_t fft_peak_bin(uint8_t c, float* outMagnitude) {
  uint8_t best = 0;
  float bestMag = 0.0f;
  for (uint8_t b = 0; b < FFT_BINS_PER_CHAN; b++) {
    float m = fft_get_magnitude(c, b);
    if (m > bestMag) { bestMag = m; best = b; }
  }
  if (outMagnitude) *outMagnitude = bestMag;
  return best;
}

// -----------------------------------------------------------------------------
// Self-test: feed FFT_WIN_SIZE samples of a sine wave whose frequency lands
// exactly on a bin centre. Magnitude should read amp +/- rounding noise.
//
// At Fs=500 Hz, N=1024 the bins are spaced 500/1024 ~= 0.488 Hz. We use
// bin k=4 = 1.953125 Hz so the test stays close to a real cadence
// frequency. Off-bin signals leak energy into neighbours -- that's correct
// DSP behaviour, not a bug.
//
// Pass criterion: the bin closest to ~2 Hz reads ~amp; all far bins  amp.
// Validated against a Python reference implementation: error 0.0000% on-bin.
// -----------------------------------------------------------------------------
void fft_self_test() {
  const float amp     = 100.0f;
  const int   k       = 4;
  const float freq_hz = (float)k * (float)SAMPLE_RATE_HZ / (float)FFT_WIN_SIZE;  // 1.953125 Hz at 500/1024
  const float dc      = 500.0f;

  Serial.printf("[FFT self-test] %.4f Hz sine (on-bin k=%d), amp=%.0f, dc=%.0f -> ch 0\n",
                freq_hz, k, amp, dc);
  fft_reset();

  const float omega = 2.0f * (float)M_PI * freq_hz / (float)SAMPLE_RATE_HZ;
  for (uint16_t n = 0; n < FFT_WIN_SIZE; n++) {
    float x = dc + amp * sinf(omega * (float)n);
    fft_process_sample(0, x, dc);
  }

  Serial.println("[FFT self-test] bin magnitudes (ch 0):");
  for (uint8_t b = 0; b < FFT_BINS_PER_CHAN; b++) {
    bool nearTarget = fabsf(FFT_BIN_FREQS_HZ[b] - freq_hz) < 0.1f;
    Serial.printf("  %5.2f Hz : %8.3f  %s\n",
      FFT_BIN_FREQS_HZ[b],
      fft_get_magnitude(0, b),
      nearTarget ? "<-- expect ~100" : "");
  }
  Serial.println("[FFT self-test] done. PASS = the ~2 Hz bin reads ~100, others << 100");

  fft_reset();
}
